Lucas-Poulos/rtk-gps-module/design/01_power.kicad_sch

## KiCad design design/01_power.kicad_sch (2026-09-28)

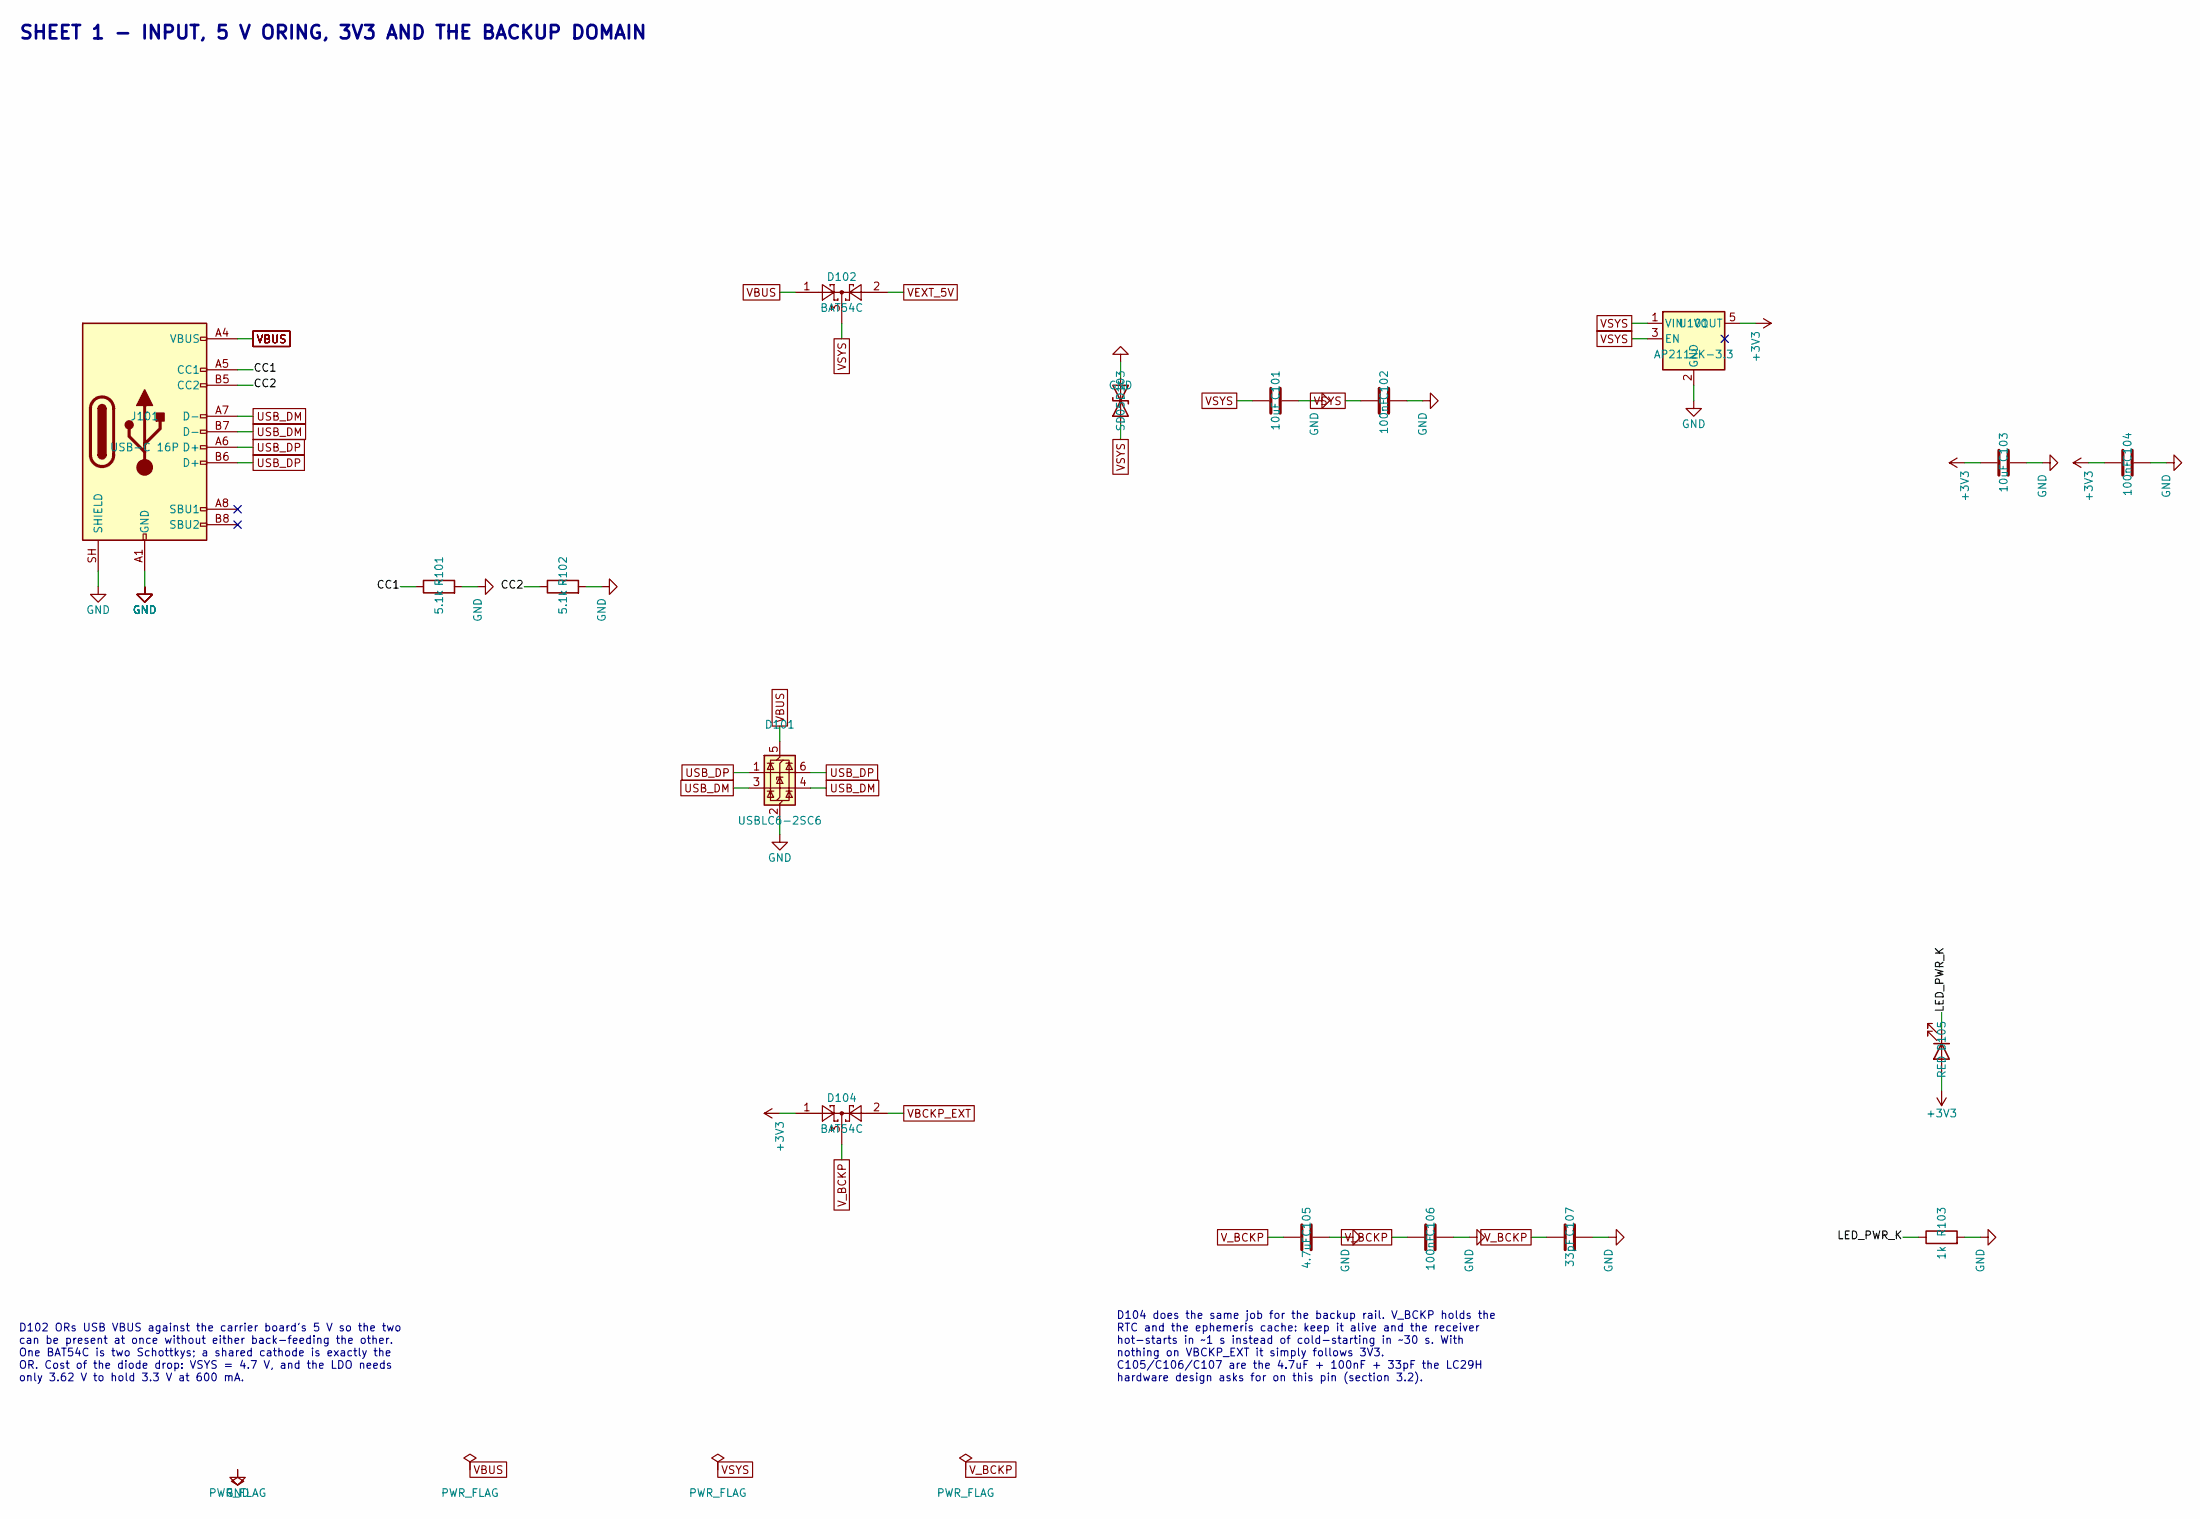
[picture p7: schematic 01_power.kicad_sch]

Parts:
C101, C103: 10uF; C_0805_2012Metric; MPN CL21A106KAYNNNE; LCSC C15850
C102, C104, C106: 100nF; C_0402_1005Metric; MPN CL05B104KO5NNNC; LCSC C1525
C105: 4.7uF; C_0603_1608Metric; MPN CL10A475KO8NNNC; LCSC C19666
C107: 33pF; C_0402_1005Metric; MPN 0402CG330J500NT; LCSC C1562
D101: USBLC6-2SC6; SOT-23-6; MPN USBLC6-2SC6; LCSC C2827654
D102, D104: BAT54C; SOT-23; MPN BAT54C; LCSC C916424
D103: SD05; D_SOD-323; MPN SD05; LCSC C502527
D105: RED; LED_0603_1608Metric; MPN KT-0603R; LCSC C2286
J101: USB-C 16P; USB_C_Receptacle_HRO_TYPE-C-31-M-12; MPN TYPE-C 16PIN 2MD(073); LCSC C2765186
R101, R102: 5.1k; R_0402_1005Metric; Tolerance 1%; MPN 0402WGF5101TCE; LCSC C25905
R103: 1k; R_0402_1005Metric; Tolerance 1%; MPN 0402WGF1001TCE; LCSC C11702
U101: AP2112K-3.3; SOT-23-5; MPN AP2112K-3.3TRG1; LCSC C23380830

Connections:
+3V3: C103.1, C104.1, D104.1, D105.2 (A), U101.5 (VOUT)
CC1: J101.A5 (CC1), R101.1
CC2: J101.B5 (CC2), R102.1
GND: C101.2, C102.2, C103.2, C104.2, C105.2, C106.2, C107.2, D101.2 (GND), D103.2 (A2), J101.A1 (GND), J101.A12 (GND), J101.B1 (GND), J101.B12 (GND), J101.SH (SHIELD), R101.2, R102.2, R103.2, U101.2 (GND)
LED_PWR_K: D105.1 (K), R103.1
USB_DM: D101.3 (I/O2), D101.4 (I/O2), J101.A7 (D-), J101.B7 (D-)
USB_DP: D101.1 (I/O1), D101.6 (I/O1), J101.A6 (D+), J101.B6 (D+)
VBCKP_EXT: D104.2
VBUS: D101.5 (VBUS), D102.1, J101.A4 (VBUS), J101.A9 (VBUS), J101.B4 (VBUS), J101.B9 (VBUS)
VEXT_5V: D102.2
VSYS: C101.1, C102.1, D102.3, D103.1 (A1), U101.1 (VIN), U101.3 (EN)
V_BCKP: C105.1, C106.1, C107.1, D104.3

Notes on the sheet:
D102 ORs USB VBUS against the carrier board's 5 V so the two can be present at once without either back-feeding the other. One BAT54C is two Schottkys; a shared cathode is exactly the OR. Cost of the diode drop: VSYS = 4.7 V, and the LDO needs only 3.62 V to hold 3.3 V at 600 mA.
SHEET 1 - INPUT, 5 V ORING, 3V3 AND THE BACKUP DOMAIN
D104 does the same job for the backup rail. V_BCKP holds the RTC and the ephemeris cache: keep it alive and the receiver hot-starts in ~1 s instead of cold-starting in ~30 s. With nothing on VBCKP_EXT it simply follows 3V3. C105/C106/C107 are the 4.7uF + 100nF + 33pF the LC29H hardware design asks 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
