Lucas-Poulos/rtk-gps-module/design/02_gnss.kicad_sch

## KiCad design design/02_gnss.kicad_sch (2026-09-28)

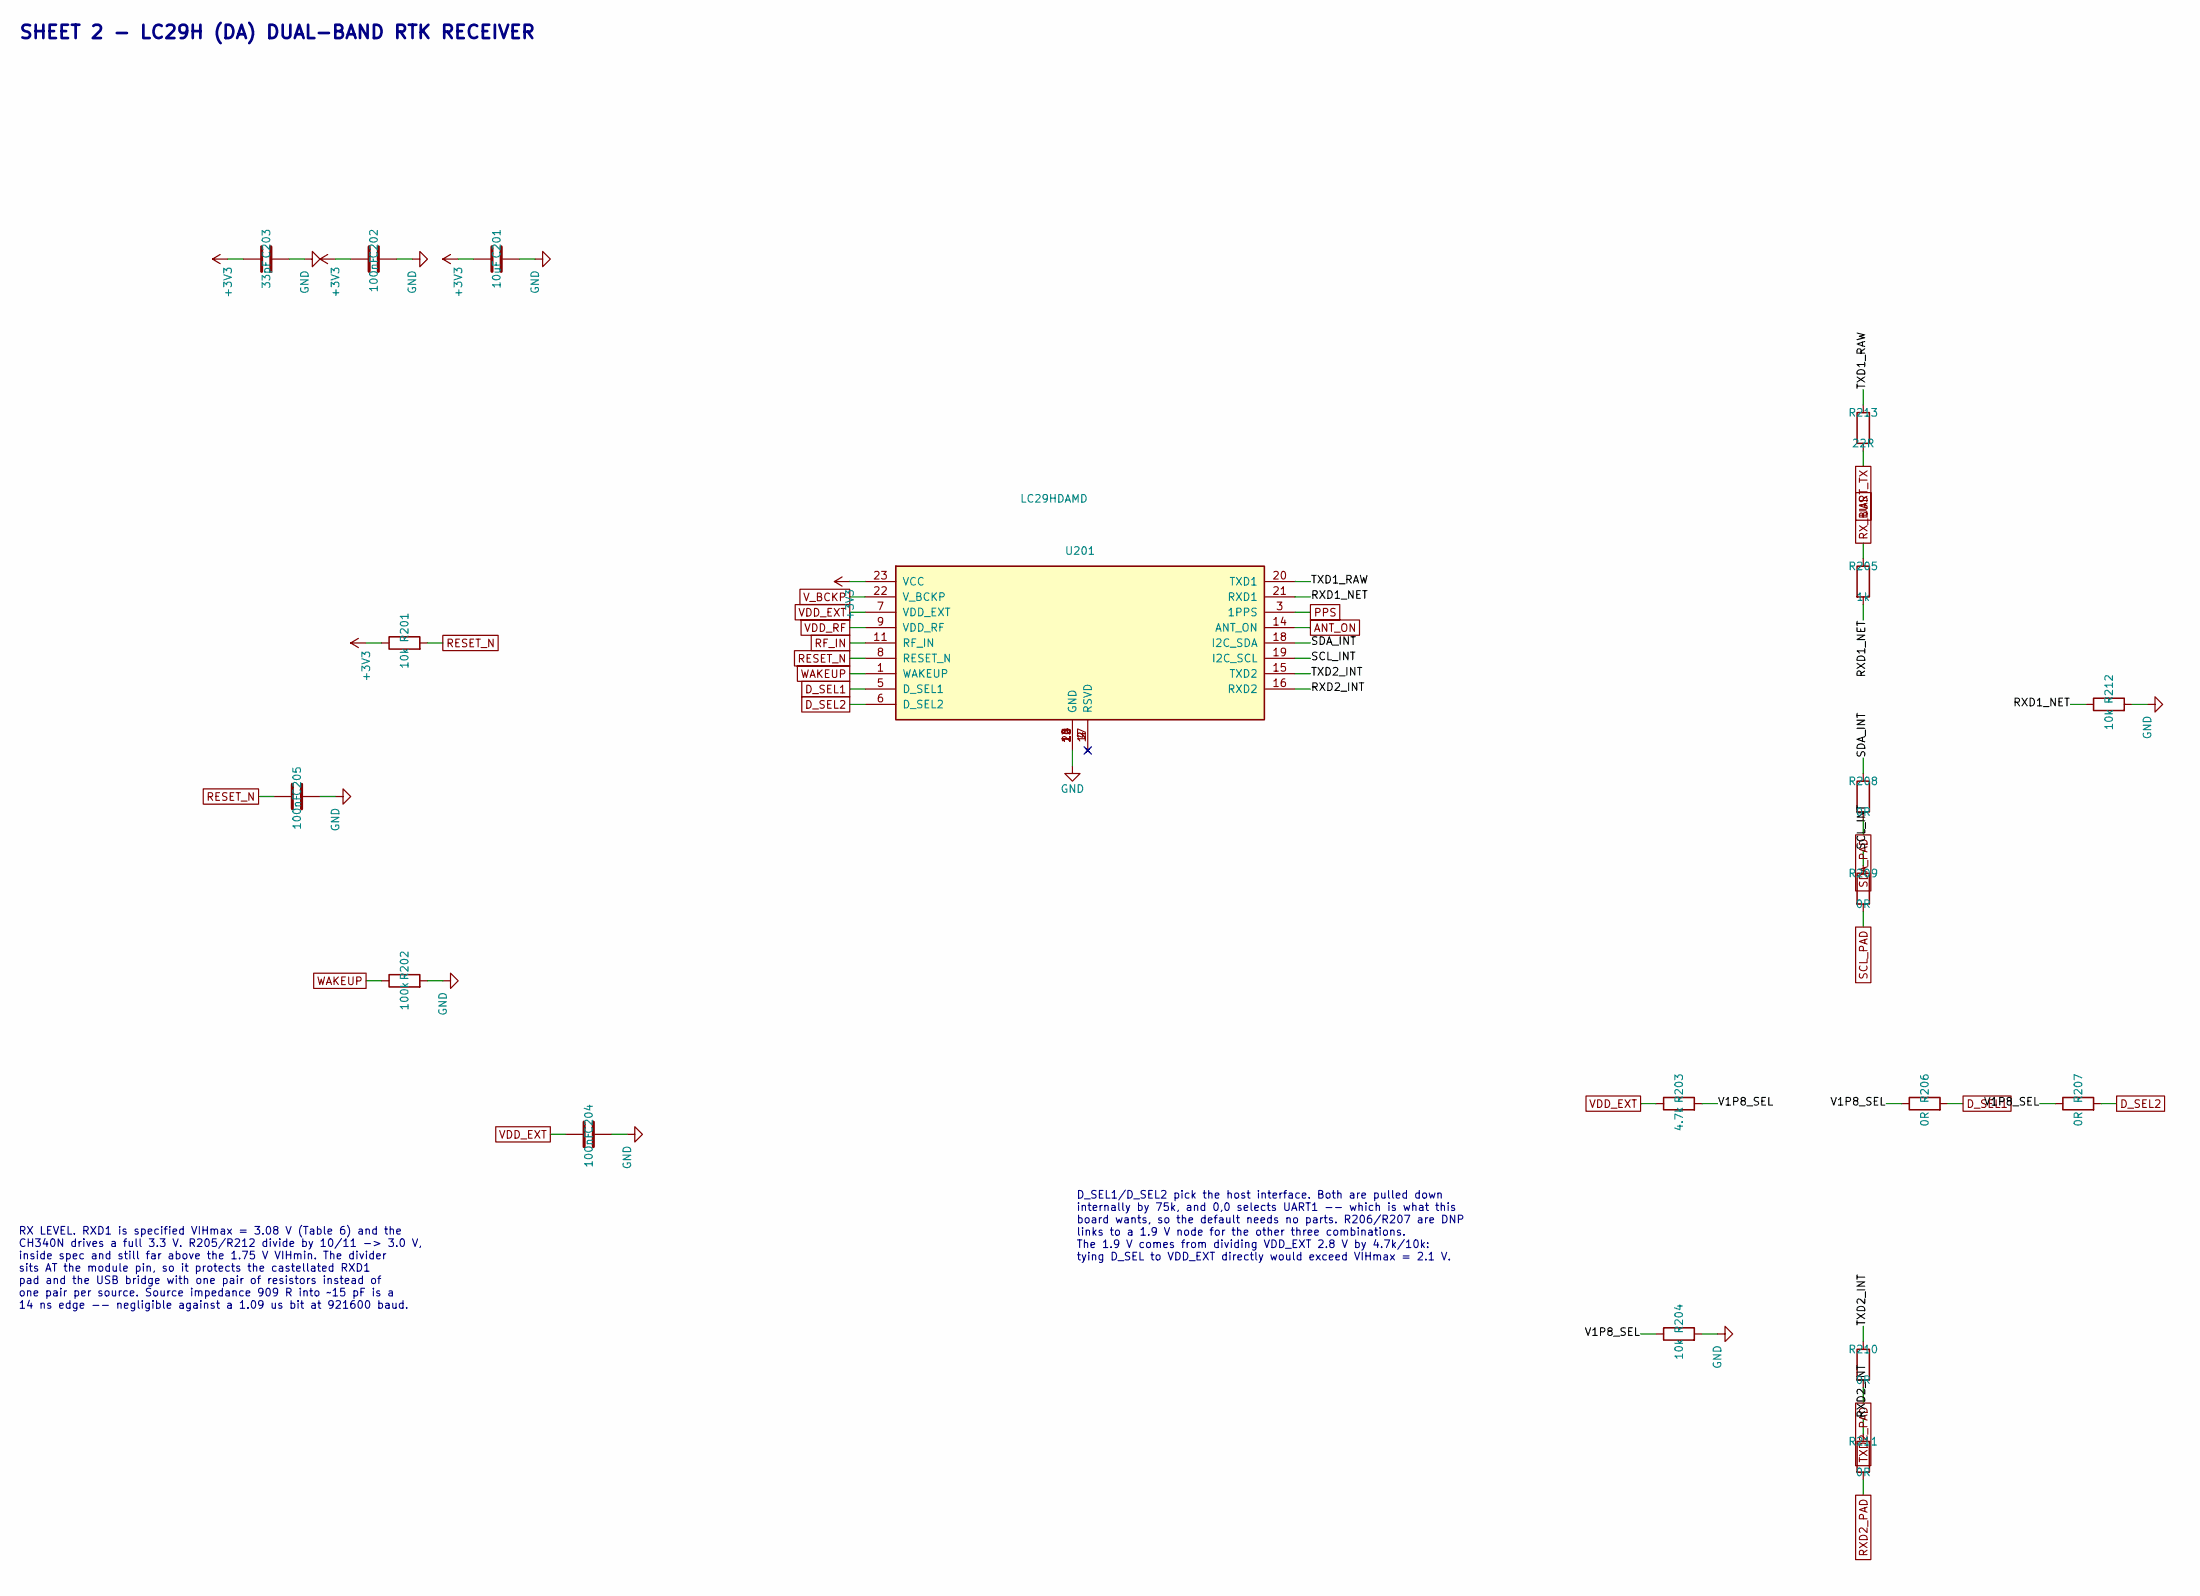
[picture p8: schematic 02_gnss.kicad_sch]

Parts:
C201: 10uF; C_0805_2012Metric; MPN CL21A106KAYNNNE; LCSC C15850
C202, C204, C205: 100nF; C_0402_1005Metric; MPN CL05B104KO5NNNC; LCSC C1525
C203: 33pF; C_0402_1005Metric; MPN 0402CG330J500NT; LCSC C1562
R201, R204, R212: 10k; R_0402_1005Metric; Tolerance 1%; MPN 0402WGF1002TCE; LCSC C25744
R202: 100k; R_0402_1005Metric; Tolerance 1%; MPN 0402WGF1003TCE; LCSC C25741
R203: 4.7k; R_0402_1005Metric; Tolerance 1%; MPN 0402WGF4701TCE; LCSC C25900
R205: 1k; R_0402_1005Metric; Tolerance 1%; MPN 0402WGF1001TCE; LCSC C11702
R206, R207, R208, R209, R210, R211: 0R; R_0402_1005Metric; Tolerance 1%; MPN 0402WGF0000TCE; LCSC C17168
R213: 22R; R_0402_1005Metric; Tolerance 1%; MPN 0402WGF220JTCE; LCSC C25092
U201: LC29HDAMD; Quectel_LC29H_LCC-24_12.2x16.0mm; MPN LC29HDAMD; LCSC C20748061

Connections:
+3V3: C201.1, C202.1, C203.1, R201.1, U201.23 (VCC)
ANT_ON: U201.14 (ANT_ON)
D_SEL1: R206.2, U201.5 (D_SEL1)
D_SEL2: R207.2, U201.6 (D_SEL2)
GND: C201.2, C202.2, C203.2, C204.2, C205.2, R202.2, R204.2, R212.2, U201.10 (GND), U201.12 (GND), U201.13 (GND), U201.24 (GND)
unnamed: U201.2 (RSVD), U201.4 (RSVD), U201.17 (RSVD)
PPS: U201.3 (1PPS)
RESET_N: C205.1, R201.2, U201.8 (RESET_N)
RF_IN: U201.11 (RF_IN)
RXD1_NET: R205.2, R212.1, U201.21 (RXD1)
RXD2_INT: R211.1, U201.16 (RXD2)
RXD2_PAD: R211.2
RX_BUS: R205.1
SCL_INT: R209.1, U201.19 (I2C_SCL)
SCL_PAD: R209.2
SDA_INT: R208.1, U201.18 (I2C_SDA)
SDA_PAD: R208.2
TXD1_RAW: R213.1, U201.20 (TXD1)
TXD2_INT: R210.1, U201.15 (TXD2)
TXD2_PAD: R210.2
UART_TX: R213.2
V1P8_SEL: R203.2, R204.1, R206.1, R207.1
VDD_EXT: C204.1, R203.1, U201.7 (VDD_EXT)
VDD_RF: U201.9 (VDD_RF)
V_BCKP: U201.22 (V_BCKP)
WAKEUP: R202.1, U201.1 (WAKEUP)

Notes on the sheet:
D_SEL1/D_SEL2 pick the host interface. Both are pulled down internally by 75k, and 0,0 selects UART1 -- which is what this board wants, so the default needs no parts. R206/R207 are DNP links to a 1.9 V node for the other three combinations. The 1.9 V comes from dividing VDD_EXT 2.8 V by 4.7k/10k: t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
RX LEVEL. RXD1 is specified VIHmax = 3.08 V (Table 6) and the CH340N drives a full 3.3 V. R205/R212 divide by 10/11 -> 3.0 V, inside spec and still far above the 1.75 V VIHmin. The divider sits AT the module pin, so it protects the castellated RXD1 pad and the USB bridge with one pair of resistors 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
SHEET 2 - LC29H (DA) DUAL-BAND RTK RECEIVER
