Lucas-Poulos/rtk-gps-module/design/03_rf.kicad_sch

## KiCad design design/03_rf.kicad_sch (2026-09-28)

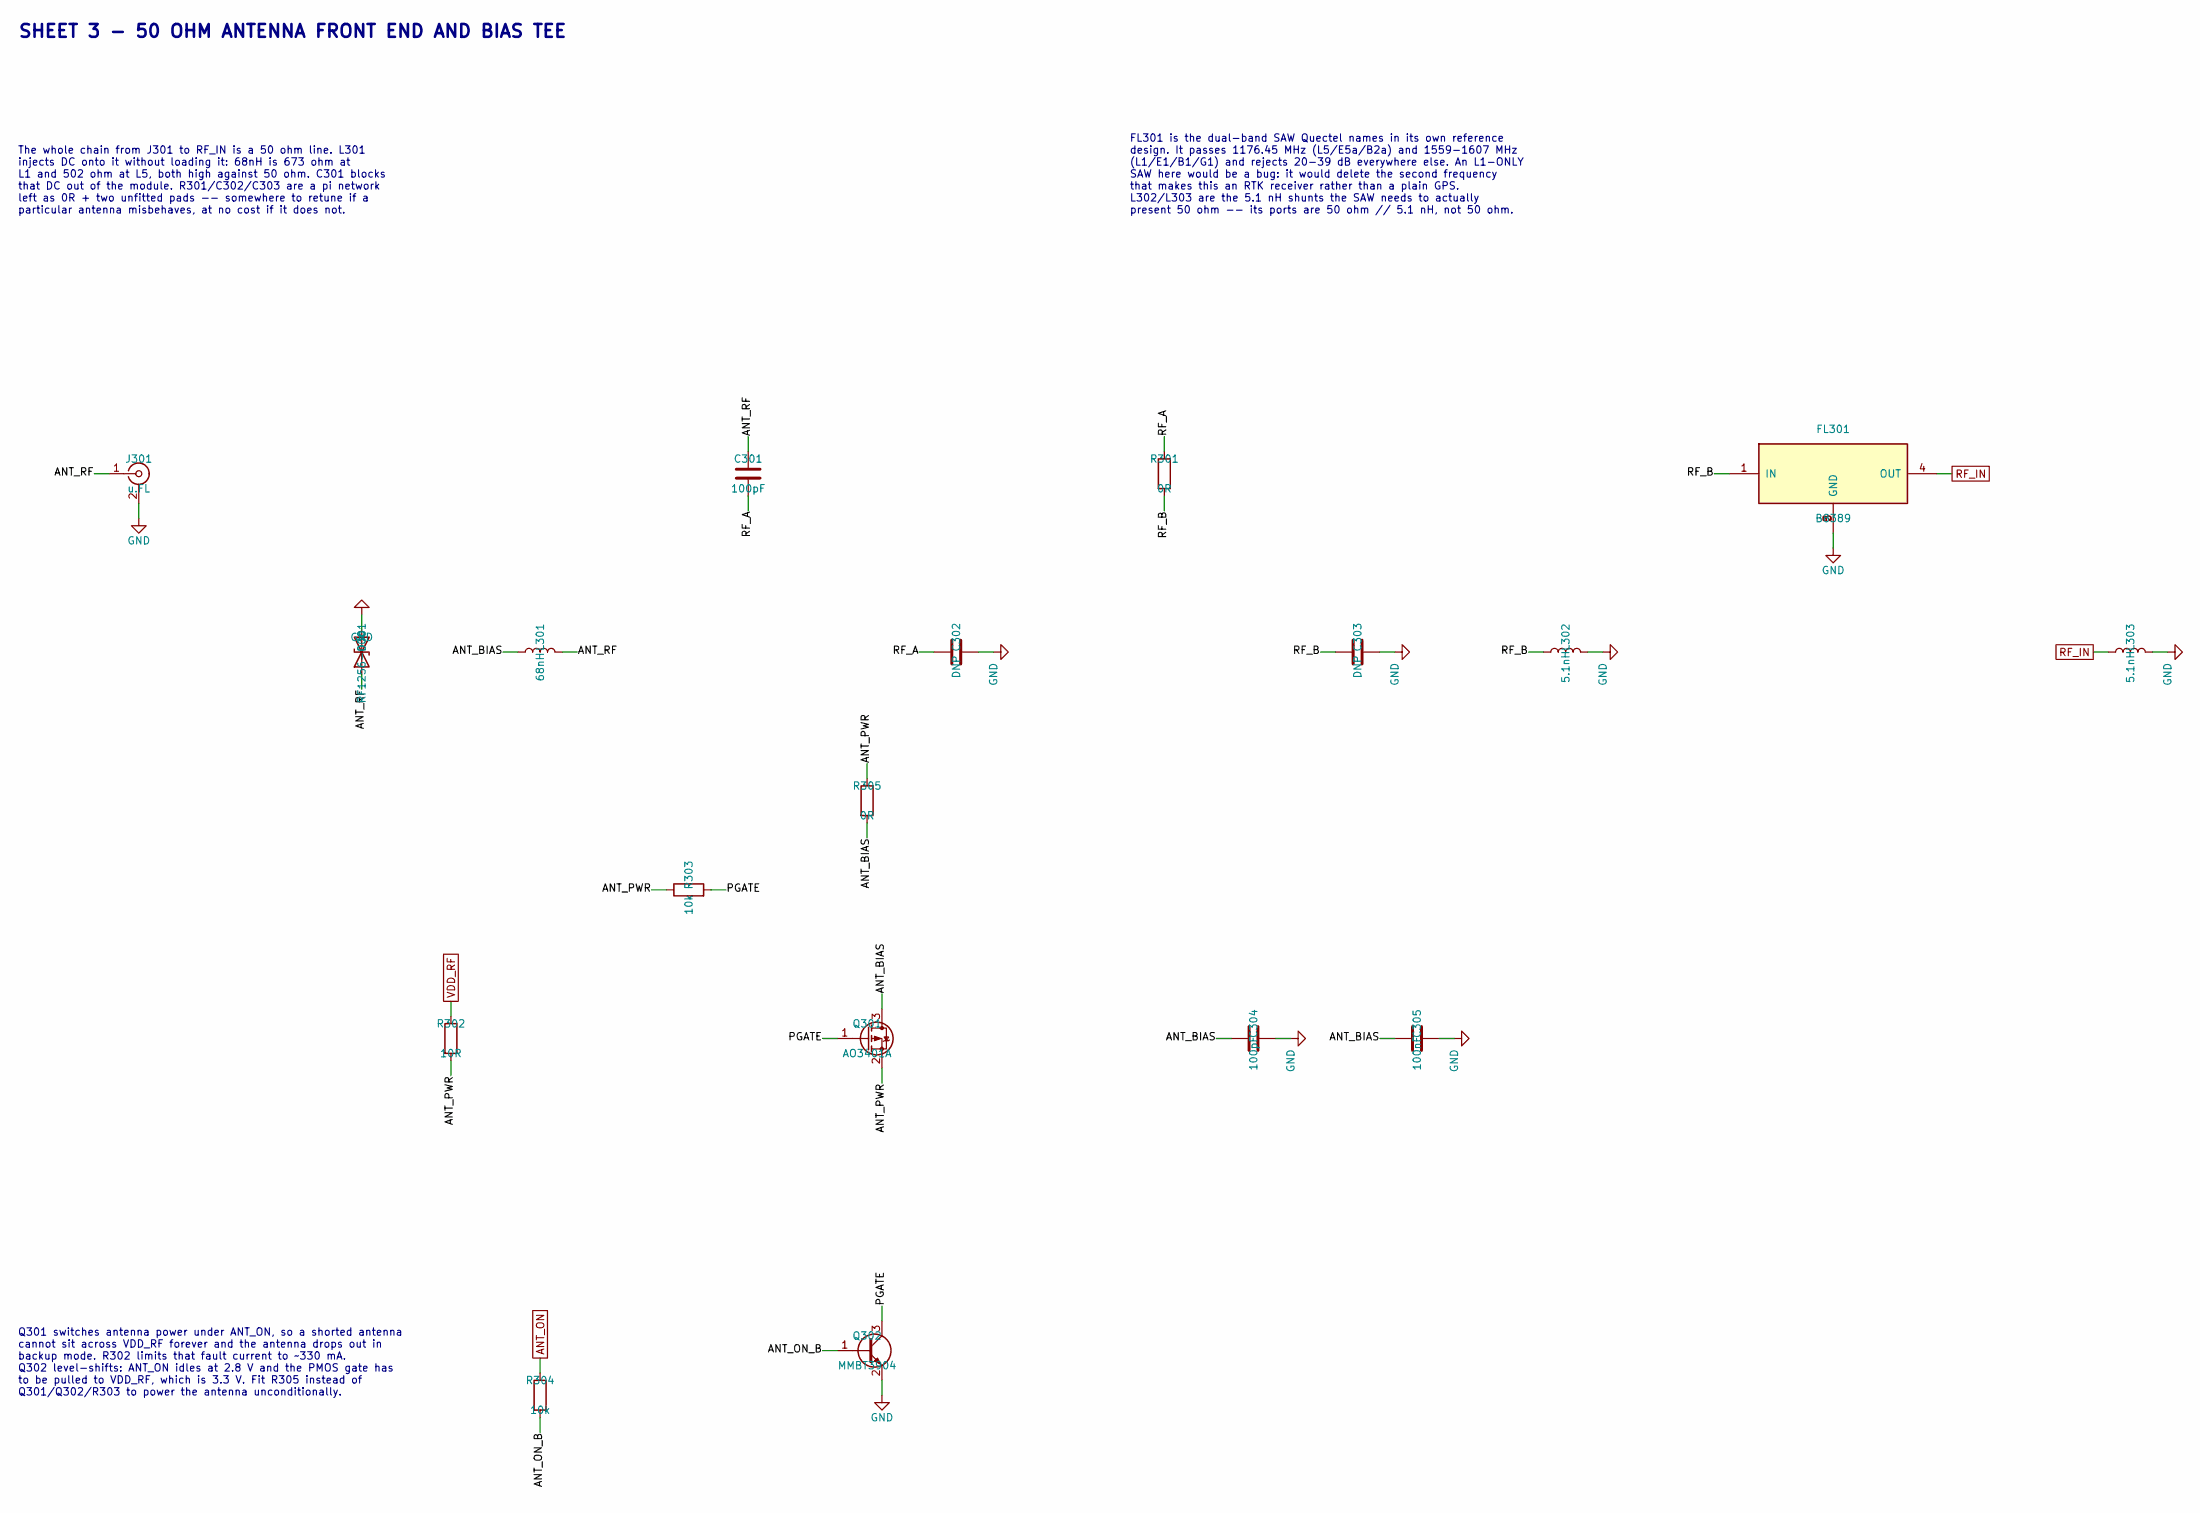
[picture p9: schematic 03_rf.kicad_sch]

Parts:
C301, C304: 100pF; C_0402_1005Metric; MPN 0402CG101J500NT; LCSC C1546
C302, C303: DNP; C_0402_1005Metric
C305: 100nF; C_0402_1005Metric; MPN CL05B104KO5NNNC; LCSC C1525
D301: RF1256-000; D_0603_1608Metric; MPN RF1256-000; LCSC C207186
FL301: B8389; SAW_RF360_SMD1411-5P_1.4x1.1mm; MPN B39162B8389P810; LCSC C5556161
J301: u.FL; U.FL_Hirose_U.FL-R-SMT-1_Vertical; MPN BWU.FL-IPEX1; LCSC C5137195
L301: 68nH; L_0402_1005Metric; MPN LQW15AN68NG00D; LCSC C108965
L302, L303: 5.1nH; L_0402_1005Metric; MPN LQW15AN5N1B00D; LCSC C408161
Q301: AO3401A; SOT-23; MPN AO3401A; LCSC C15127
Q302: MMBT3904; SOT-23; MPN MMBT3904; LCSC C20526
R301, R305: 0R; R_0402_1005Metric; Tolerance 1%; MPN 0402WGF0000TCE; LCSC C17168
R302: 10R; R_0402_1005Metric; Tolerance 1%; MPN 0402WGF100JTCE; LCSC C25077
R303, R304: 10k; R_0402_1005Metric; Tolerance 1%; MPN 0402WGF1002TCE; LCSC C25744

Connections:
ANT_BIAS: C304.1, C305.1, L301.1, Q301.3 (D), R305.2
ANT_ON: R304.1
ANT_ON_B: Q302.1 (B), R304.2
ANT_PWR: Q301.2 (S), R302.2, R303.1, R305.1
ANT_RF: C301.1, D301.1 (A1), J301.1 (In), L301.2
GND: C302.2, C303.2, C304.2, C305.2, D301.2 (A2), FL301.2 (GND), FL301.3 (GND), FL301.5 (GND), J301.2 (Ext), L302.2, L303.2, Q302.2 (E)
PGATE: Q301.1 (G), Q302.3 (C), R303.2
RF_A: C301.2, C302.1, R301.1
RF_B: C303.1, FL301.1 (IN), L302.1, R301.2
RF_IN: FL301.4 (OUT), L303.1
VDD_RF: R302.1

Notes on the sheet:
Q301 switches antenna power under ANT_ON, so a shorted antenna cannot sit across VDD_RF forever and the antenna drops out in backup mode. R302 limits that fault current to ~330 mA. Q302 level-shifts: ANT_ON idles at 2.8 V and the PMOS gate has to be pulled to VDD_RF, which is 3.3 V. Fit R305 instea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
FL301 is the dual-band SAW Quectel names in its own reference design. It passes 1176.45 MHz (L5/E5a/B2a) and 1559-1607 MHz (L1/E1/B1/G1) and rejects 20-39 dB everywhere else. An L1-ONLY SAW here would be a bug: it would delete the second frequency that makes this an RTK receiver rather than a plain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
The whole chain from J301 to RF_IN is a 50 ohm line. L301 injects DC onto it without loading it: 68nH is 673 ohm at L1 and 502 ohm at L5, both high against 50 ohm. C301 blocks that DC out of the module. R301/C302/C303 are a pi network left as 0R + two unfitted pads -- somewhere to retune if a parti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
SHEET 3 - 50 OHM ANTENNA FRONT END AND BIAS TEE
