Lucas-Poulos/rtk-gps-module/design/04_usb.kicad_sch

## KiCad design design/04_usb.kicad_sch (2026-09-28)

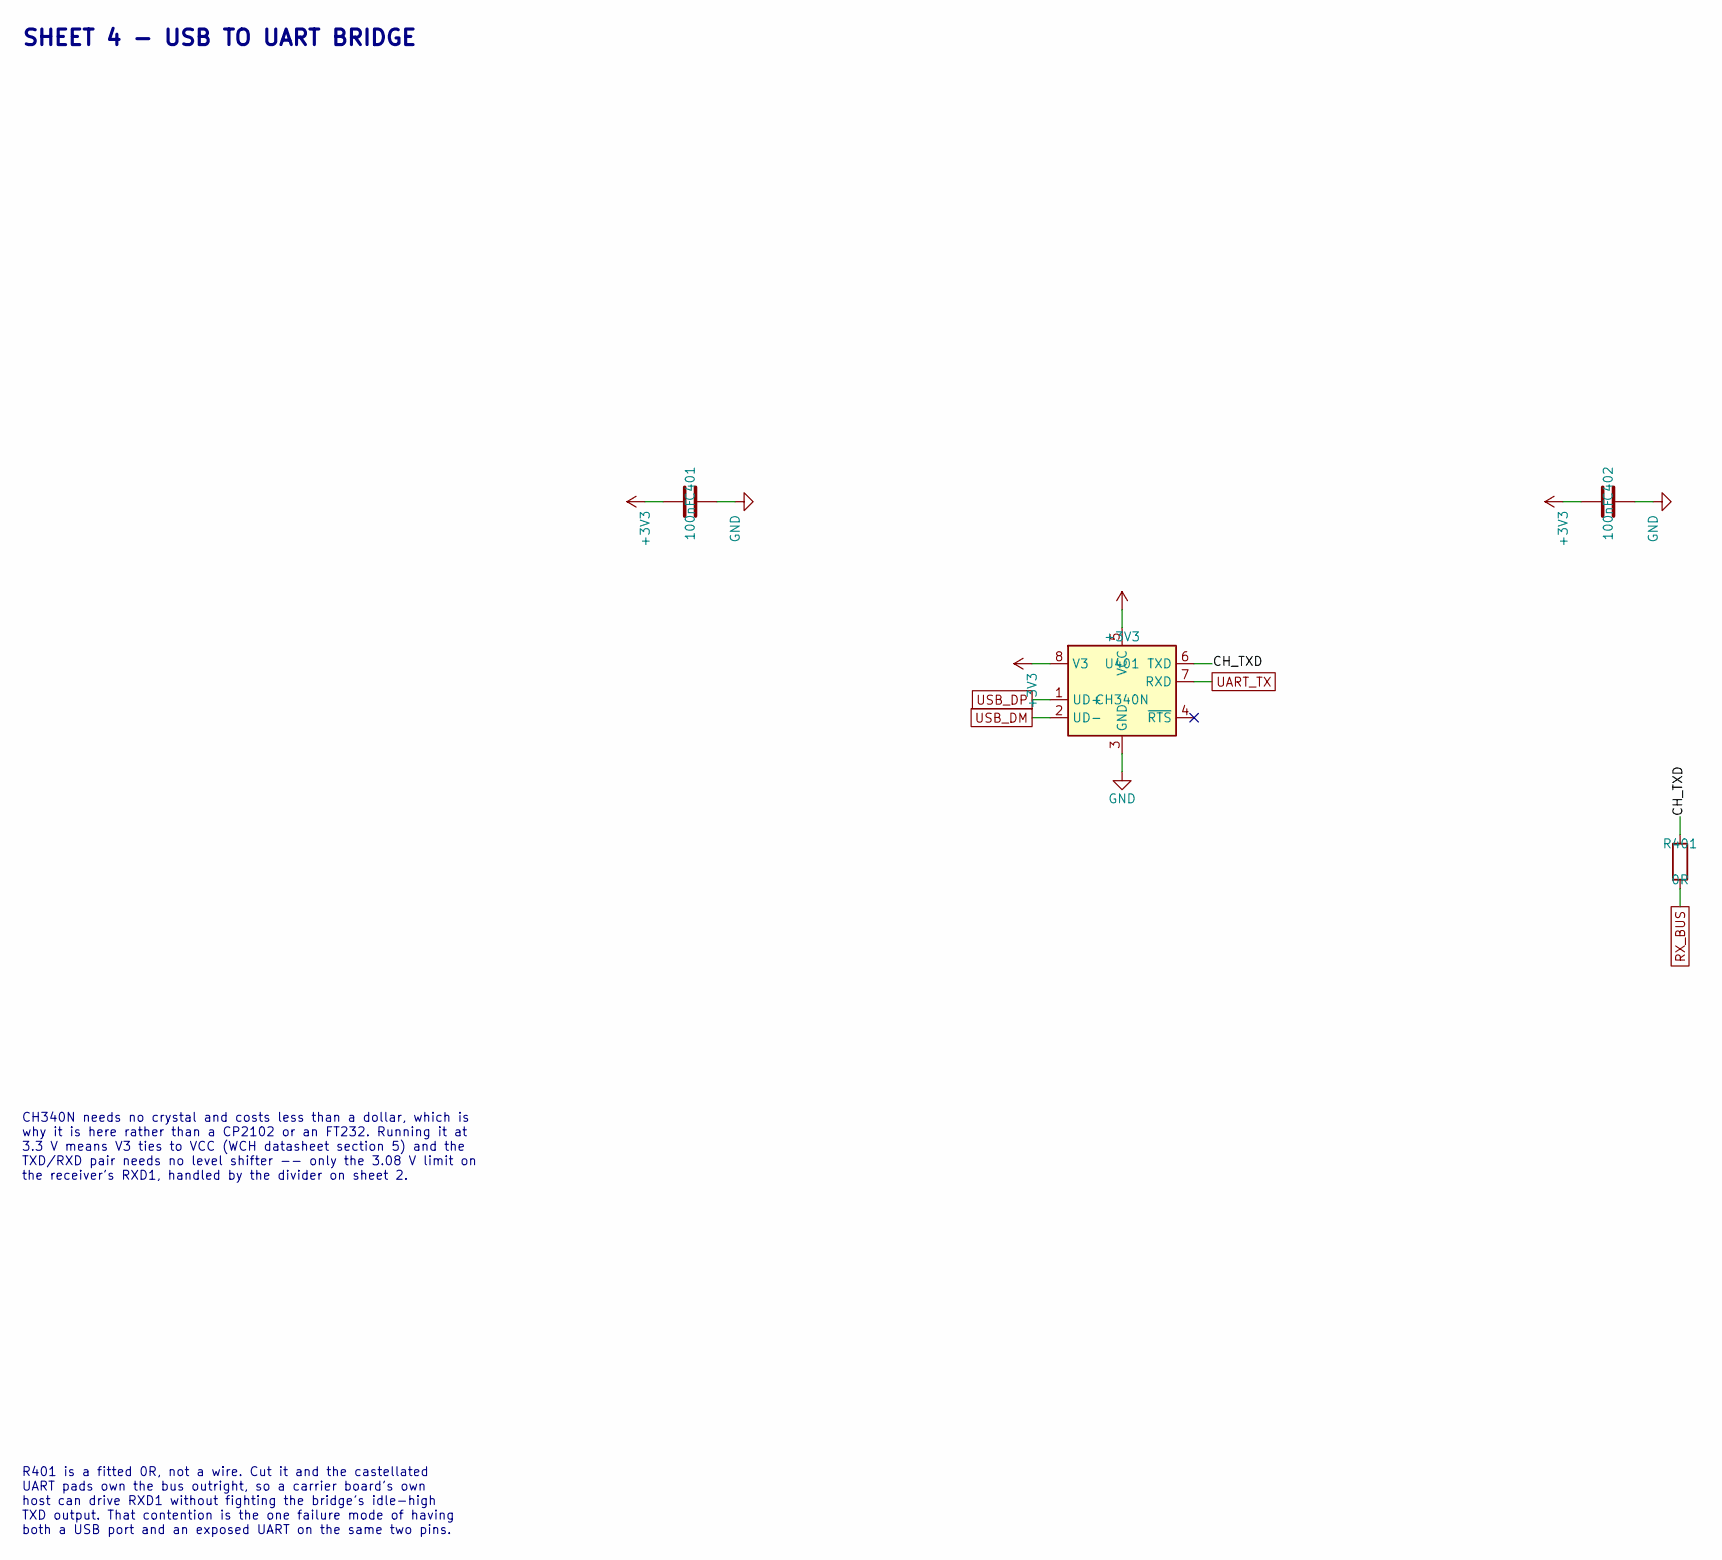
[picture p10: schematic 04_usb.kicad_sch]

Parts:
C401, C402: 100nF; C_0402_1005Metric; MPN CL05B104KO5NNNC; LCSC C1525
R401: 0R; R_0402_1005Metric; Tolerance 1%; MPN 0402WGF0000TCE; LCSC C17168
U401: CH340N; SOIC-8_3.9x4.9mm_P1.27mm; MPN CH340N; LCSC C2977777

Connections:
+3V3: C401.1, C402.1, U401.5 (VCC), U401.8 (V3)
CH_TXD: R401.1, U401.6 (TXD)
GND: C401.2, C402.2, U401.3 (GND)
RX_BUS: R401.2
UART_TX: U401.7 (RXD)
USB_DM: U401.2 (UD-)
USB_DP: U401.1 (UD+)

Notes on the sheet:
R401 is a fitted 0R, not a wire. Cut it and the castellated UART pads own the bus outright, so a carrier board's own host can drive RXD1 without fighting the bridge's idle-high TXD output. That contention is the one failure mode of having both a USB port and an exposed UART on the same two pins.
CH340N needs no crystal and costs less than a dollar, which is why it is here rather than a CP2102 or an FT232. Running it at 3.3 V means V3 ties to VCC (WCH datasheet section 5) and the TXD/RXD pair needs no level shifter -- only the 3.08 V limit on the receiver's RXD1, handled by the divider on s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
SHEET 4 - USB TO UART BRIDGE
