Lucas-Poulos/rtk-gps-module/design/05_io.kicad_sch

## KiCad design design/05_io.kicad_sch (2026-09-28)

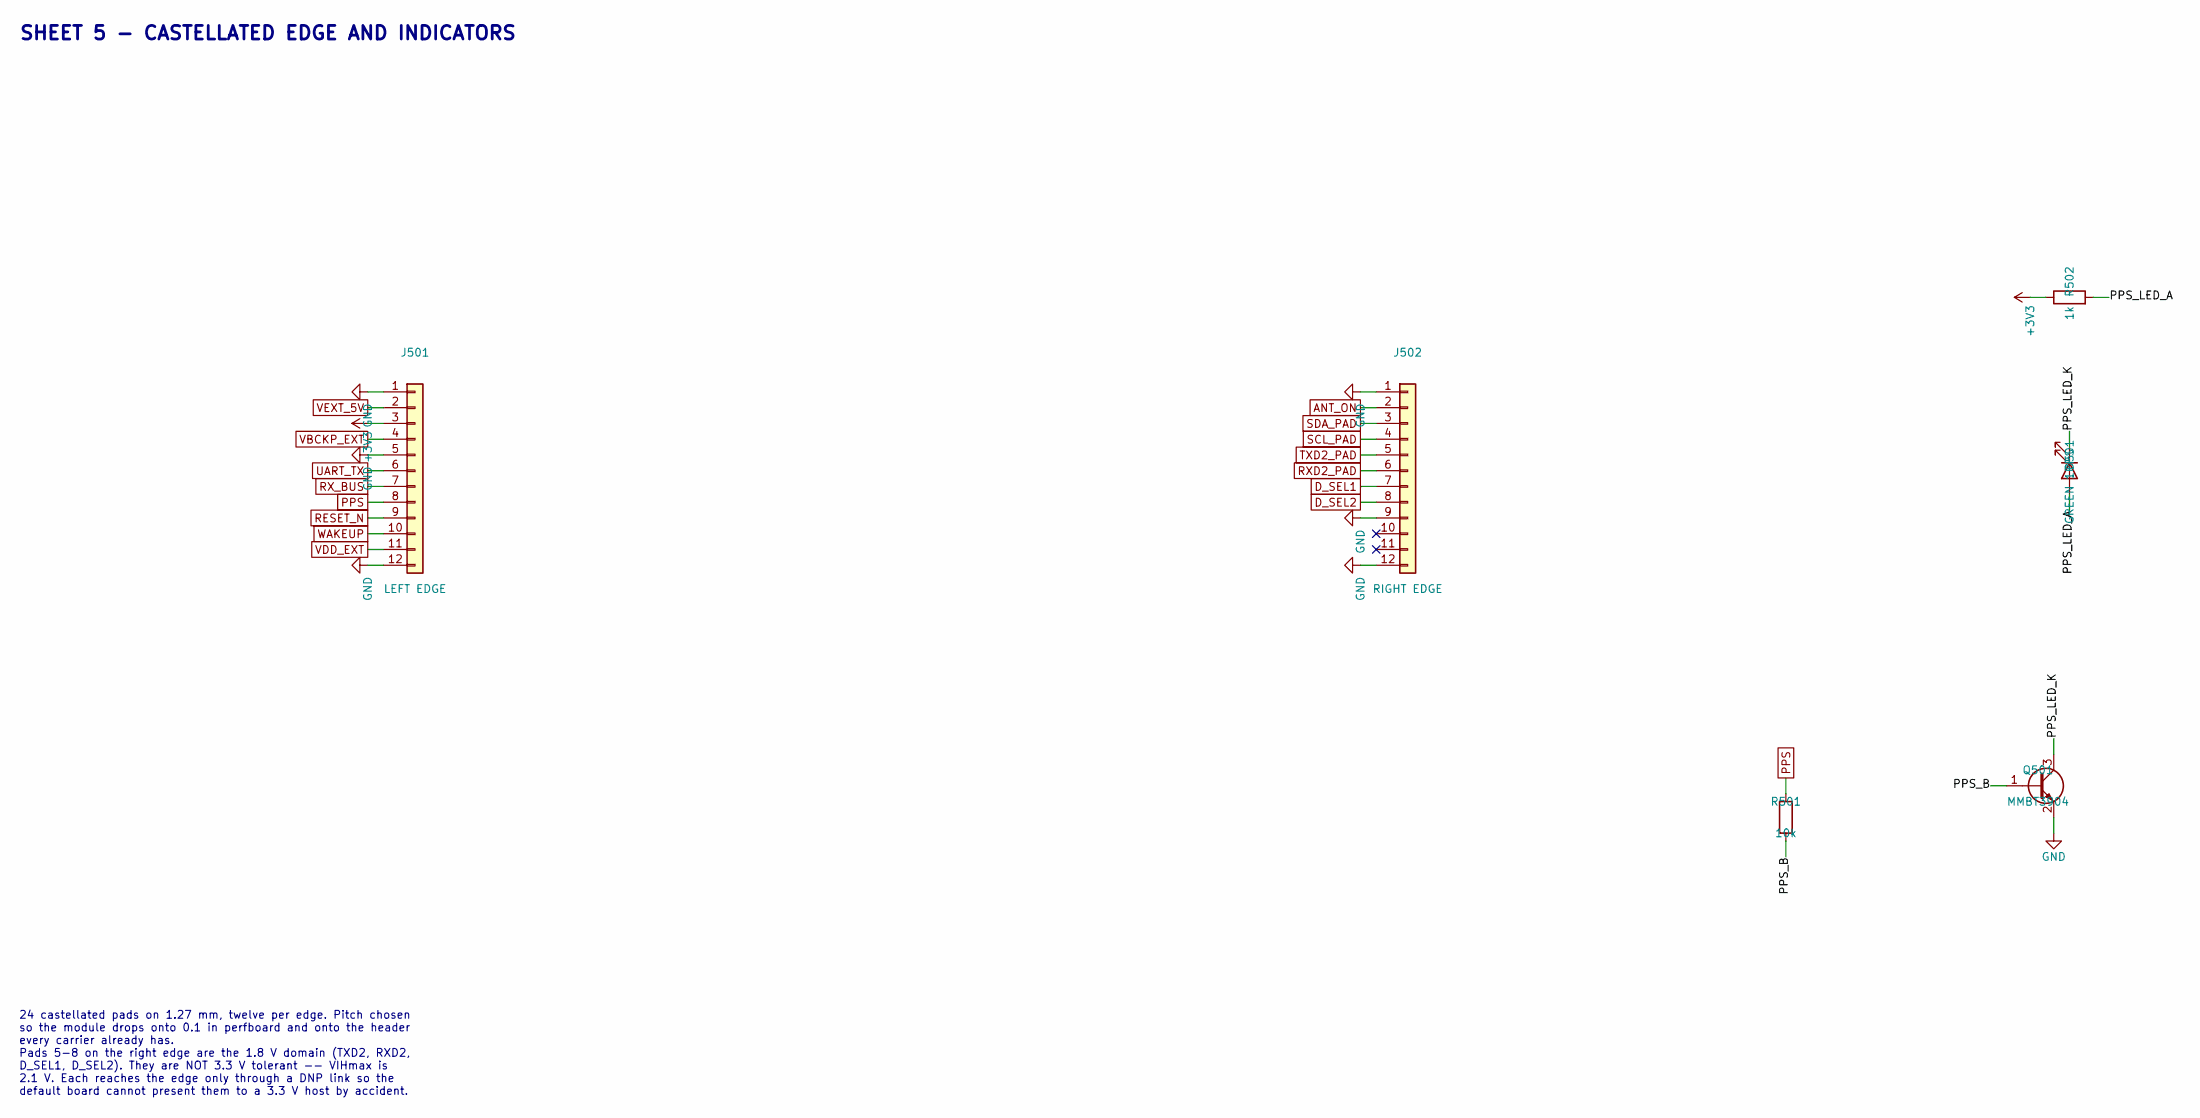
[picture p11: schematic 05_io.kicad_sch]

Parts:
D501: GREEN 1PPS; LED_0603_1608Metric; MPN KT-0603G; LCSC C12624
J501: LEFT EDGE; Castellated_1x12_P1.27mm
J502: RIGHT EDGE; Castellated_1x12_P1.27mm
Q501: MMBT3904; SOT-23; MPN MMBT3904; LCSC C20526
R501: 10k; R_0402_1005Metric; Tolerance 1%; MPN 0402WGF1002TCE; LCSC C25744
R502: 1k; R_0402_1005Metric; Tolerance 1%; MPN 0402WGF1001TCE; LCSC C11702

Connections:
+3V3: J501.3, R502.1
ANT_ON: J502.2
D_SEL1: J502.7
D_SEL2: J502.8
GND: J501.1, J501.5, J501.12, J502.1, J502.9, J502.12, Q501.2 (E)
PPS: J501.8, R501.1
PPS_B: Q501.1 (B), R501.2
PPS_LED_A: D501.2 (A), R502.2
PPS_LED_K: D501.1 (K), Q501.3 (C)
RESET_N: J501.9
RXD2_PAD: J502.6
RX_BUS: J501.7
SCL_PAD: J502.4
SDA_PAD: J502.3
TXD2_PAD: J502.5
UART_TX: J501.6
VBCKP_EXT: J501.4
VDD_EXT: J501.11
VEXT_5V: J501.2
WAKEUP: J501.10

Notes on the sheet:
24 castellated pads on 1.27 mm, twelve per edge. Pitch chosen so the module drops onto 0.1 in perfboard and onto the header every carrier already has. Pads 5-8 on the right edge are the 1.8 V domain (TXD2, RXD2, D_SEL1, D_SEL2). They are NOT 3.3 V tolerant -- VIHmax is 2.1 V. Each reaches the edge 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
SHEET 5 - CASTELLATED EDGE AND INDICATORS
